dwkennedy/inclinometer-display/GroteskBold32x64.c

// GroteskBold32x64.c
// Font type    : Full (95 characters)
// Font size    : 32x64 pixels
// Memory usage : 24324 bytes

#if defined(__AVR__)
    #include <avr/pgmspace.h>
    #define fontdatatype const uint8_t
#elif defined(__PIC32MX__)
    #define PROGMEM
    #define fontdatatype const unsigned char
#elif defined(__arm__)
    #define PROGMEM
    #define fontdatatype const unsigned char
#endif

fontdatatype GroteskBold32x64[24324] PROGMEM={
0x20,0x40,0x20,0x5F,
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
